rweather/UE1-TTL/images/kicad-3d-clock-board.png

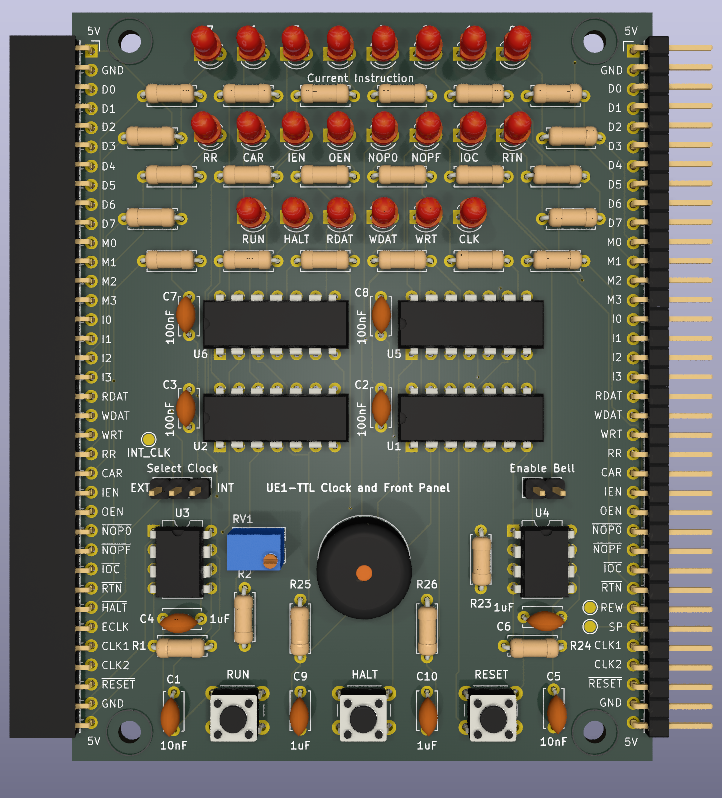
images/kicad-3d-clock-board.png
