rweather/UE1-TTL/images/kicad-3d-cpu-board.png

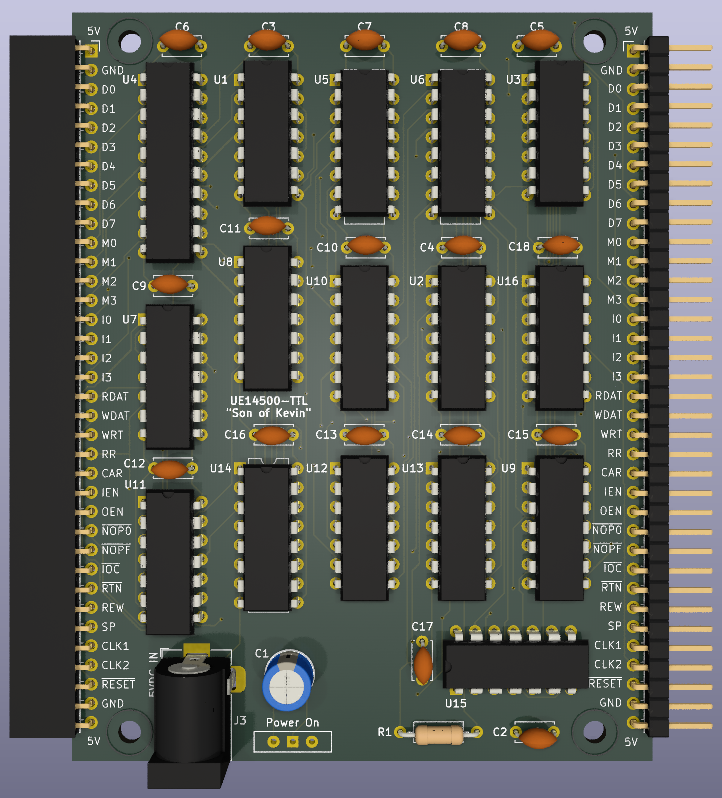
images/kicad-3d-cpu-board.png
