rweather/UE1-TTL/images/kicad-3d-full-computer.png

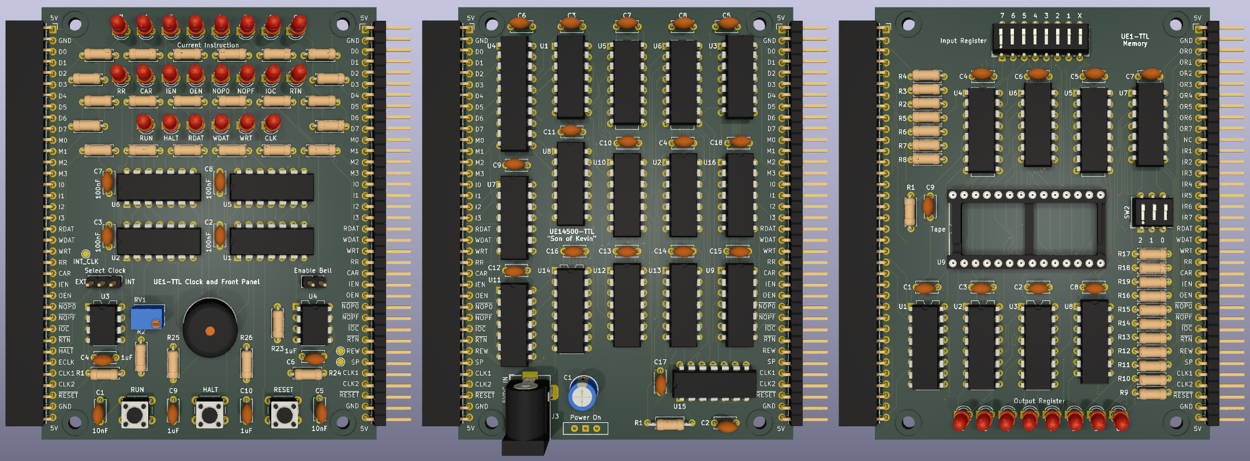
images/kicad-3d-full-computer.png
