rweather/UE1-TTL/programs/RABBIT.ASM

; Generated automatically by "rabbit-gen.py"
ONE  SR0
IEN  RR
OEN  RR
STOC OR0
STO  OR1
STOC OR2
; Command 0x0C01
STOC OR1
STO  OR2
STOC OR2
STO  OR2
STOC OR2
STO  OR2
STOC OR2
STO  OR2
STOC OR2
STO  OR0
STO  OR2
STOC OR2
STO  OR2
STOC OR2
STOC OR0
STO  OR2
STOC OR2
STO  OR2
STOC OR2
STO  OR2
STOC OR2
STO  OR2
STOC OR2
STO  OR2
STOC OR2
STO  OR2
STOC OR2
STO  OR2
STOC OR2
STO  OR2
STOC OR2
STO  OR2
STOC OR2
STO  OR0
STO  OR2
STOC OR2
STO  OR1
; Command 0x0F00
STOC OR1
STO  OR2
STOC OR2
STO  OR2
STOC OR2
STO  OR2
STOC OR2
STO  OR2
STOC OR2
STO  OR2
STOC OR2
STO  OR2
STOC OR2
STO  OR2
STOC OR2
STO  OR2
STOC OR2
STOC OR0
STO  OR2
STOC OR2
STO  OR2
STOC OR2
STO  OR2
STOC OR2
STO  OR2
STOC OR2
STO  OR2
STOC OR2
STO  OR2
STOC OR2
STO  OR2
STOC OR2
STO  OR2
STOC OR2
STO  OR1
; Command 0x0900
STOC OR1
STO  OR2
STOC OR2
STO  OR2
STOC OR2
STO  OR2
STOC OR2
STO  OR2
STOC OR2
STO  OR0
STO  OR2
STOC OR2
STOC OR0
STO  OR2
STOC OR2
STO  OR2
STOC OR2
STO  OR0
STO  OR2
STOC OR2
STOC OR0
STO  OR2
STOC OR2
STO  OR2
STOC OR2
STO  OR2
STOC OR2
STO  OR2
STOC OR2
STO  OR2
STOC OR2
STO  OR2
STOC OR2
STO  OR2
STOC OR2
STO  OR2
STOC OR2
STO  OR1
; Command 0x0B07
STOC OR1
STO  OR2
STOC OR2
STO  OR2
STOC OR2
STO  OR2
STOC OR2
STO  OR2
STOC OR2
STO  OR0
STO  OR2
STOC OR2
STOC OR0
STO  OR2
STOC OR2
STO  OR0
STO  OR2
STOC OR2
STO  OR2
STOC OR2
STOC OR0
STO  OR2
STOC OR2
STO  OR2
STOC OR2
STO  OR2
STOC OR2
STO  OR2
STOC OR2
STO  OR2
STOC OR2
STO  OR0
STO  OR2
STOC OR2
STO  OR2
STOC OR2
STO  OR2
STOC OR2
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
STO  OR2
STOC OR2
STOC OR0
STO  OR2
STOC OR2
STO  OR0
STO  OR2
STOC OR2
STOC OR0
STO  OR2
STOC OR2
STO  OR1
; Command 0x0382
STOC OR1
STO  OR2
STOC OR2
STO  OR2
STOC OR2
STO  OR2
STOC OR2
STO  OR2
STOC OR2
STO  OR2
STOC OR2
STO  OR2
STOC OR2
STO  OR0
STO  OR2
STOC OR2
STO  OR2
STOC OR2
STO  OR2
STOC OR2
STOC OR0
STO  OR2
STOC OR2
STO  OR2
STOC OR2
STO  OR2
STOC OR2
STO  OR2
STOC OR2
STO  OR2
STOC OR2
STO  OR0
STO  OR2
STOC OR2
STOC OR0
STO  OR2
STOC OR2
STO  OR1
; Command 0x0292
STOC OR1
STO  OR2
STOC OR2
STO  OR2
STOC OR2
STO  OR2
STOC OR2
STO  OR2
STOC OR2
STO  OR2
STOC OR2
STO  OR2
STOC OR2
STO  OR0
STO  OR2
STOC OR2
STOC OR0
STO  OR2
STOC OR2
STO  OR0
STO  OR2
STOC OR2
STOC OR0
STO  OR2
STOC OR2
STO  OR2
STOC OR2
STO  OR0
STO  OR2
STOC OR2
STOC OR0
STO  OR2
STOC OR2
STO  OR2
STOC OR2
STO  OR0
STO  OR2
STOC OR2
STOC OR0
STO  OR2
STOC OR2
STO  OR1
; Command 0x017C
STOC OR1
STO  OR2
STOC OR2
STO  OR2
STOC OR2
STO  OR2
STOC OR2
STO  OR2
STOC OR2
STO  OR2
STOC OR2
STO  OR2
STOC OR2
STO  OR2
STOC OR2
STO  OR0
STO  OR2
STOC OR2
STOC OR0
STO  OR2
STOC OR2
STO  OR0
STO  OR2
STOC OR2
STO  OR2
STOC OR2
STO  OR2
STOC OR2
STO  OR2
STOC OR2
STO  OR2
STOC OR2
STOC OR0
STO  OR2
STOC OR2
STO  OR2
STOC OR2
STO  OR1
IOC  SR0
NOPF SR0
